SaifYasir/PicoWOL/src/wifi/wifi.c

#include <string.h>

#include "pico/stdlib.h"
#include "pico/cyw43_arch.h"
#include "pico/util/queue.h"

#include "wifi.h"
#include "wol/wol.h"

#include "lwip/pbuf.h"
#include "lwip/udp.h"
#include "lwip/netif.h"
#include "lwip/ip4.h"


machine_stack* default_udp_polling_machine_stack = NULL;
struct udp_pcb* pcb = NULL;

int send_wol_packet_string(char* mac_address_string);
int send_wol_packet(machine* machine);

int initialise_udp_pcb(){
    pcb = udp_new();
    if(udp_bind(pcb, IP_ADDR_ANY, UDP_PORT_NUMBER) == ERR_USE)
    {
        return ERR_USE;
    }
}

int start_wifi(wifi_credential* wifi_credential){
    cyw43_arch_enable_sta_mode();
    return cyw43_arch_wifi_connect_blocking(
        wifi_credential->ssid,
        wifi_credential->ssid_password,
        CYW43_AUTH_WPA2_AES_PSK);
}

void recieve_packet_server(void *arg, struct udp_pcb *pcb, struct pbuf *p, const ip_addr_t *addr, u16_t port){
    // Decipher packet into 1 of 3 options,
    // index, string, mac address
    printf("Received packet: %s",p->payload);
    char first_char = *((char*)(p->payload));
    if (first_char == INDEX_SERVER_DELIMITER)
    {
        // assume this means index
        int index = atoi((char*)(p->payload)+1);
        machine* machine = get_machine_at_index(default_wol_profiles,index);

        //Add packet to polling thing
        push_to_machine_stack(&default_udp_polling_machine_stack,machine);
    }
    else if(first_char == STRING_SERVER_DELIMITER){
        uint8_t machine_profile_size = get_machine_stack_amount(default_wol_profiles);
        for (size_t i = 0; i < machine_profile_size; i++)
        {
            machine* machine = get_machine_at_index(default_wol_profiles,i);
            char* machine_name = machine->machine_name;
            printf("\nString to compare is %s",(char*)(p->payload)+1);
            printf("\nMachine name is: %s",machine_name);

            printf("Rando output %s",strstr((char*)(p->payload),machine_name));
            if(strstr(machine_name,(char*)(p->payload) + 1) != NULL){
                send_wol_packet(machine);
            }
        }
    }
    else if(first_char == MAC_SERVER_DELIMITER){
        send_wol_packet_string((char*)(p->payload)+1);
        // assume mac address is given in straight order IE A61421
    }
    
}

int start_udp_server(){
    if(pcb == NULL){
        initialise_udp_pcb();
    }
    udp_recv(pcb,recieve_packet_server,NULL);
}

int pico_get_port_number(){
    return UDP_PORT_NUMBER;
}

void pico_get_mac_address(uint8_t mac[6]){
    cyw43_wifi_get_mac(&cyw43_state,CYW43_ITF_STA,mac);
}

void pico_get_ip_address(char* data){
    u32_t addr = netif_default->ip_addr.addr  & netif_default->netmask.addr;
    ip4_addr_t* ip_address = netif_ip4_addr(netif_default);
    char* ip_address_str = ipaddr_ntoa(ip_address);
    memcpy(data,ip_address_str,strlen(ip_address_str) + 1);
}


int send_wol_packet(machine* machine){
    uint8_t wol_packet[MAGIC_PACKET_BYTES];
    get_magic_packet(machine,wol_packet);

    if(pcb == NULL){
        initialise_udp_pcb();
    }

    ip_addr_t target_addr;
    ip_addr_t broadcast_address;
    
    // get broadcast address
    broadcast_address.addr = (netif_default->ip_addr.addr & netif_default->netmask.addr) | ~netif_default->netmask.addr;
    udp_connect(pcb,&broadcast_address,UDP_PORT_NUMBER);

    struct pbuf *p = pbuf_alloc(PBUF_TRANSPORT,MAGIC_PACKET_BYTES,PBUF_RAM);
    pbuf_take(p,wol_packet,MAGIC_PACKET_BYTES);
    
    err_t er = udp_send(pcb,p);
    cyw43_arch_poll();

    pbuf_free(p);
    udp_disconnect(pcb);
    return er;
}

int send_wol_packet_string(char* mac_address_string){
    uint8_t wol_packet[MAGIC_PACKET_BYTES];
    uint8_t mac_address[6];

    size_t hex_string_length = strlen(mac_address_string);
    printf("mac address is %s",mac_address_string);
    printf("Size is %d",sizeof(mac_address) * 2);
    if(hex_string_length != (sizeof(mac_address) * 2)){
       printf("Hex string to byte array invalid input!");
       return 1;
    }
    for(size_t i = 0; i < hex_string_length; i += 2){
        sscanf(mac_address_string + i, "%2hhx", &mac_address[i/2]);
    }

    get_magic_packet_mac_addr(mac_address,wol_packet);

    if(pcb == NULL){
        initialise_udp_pcb();
    }

    ip_addr_t target_addr;
    ip_addr_t broadcast_address;
    
    // get broadcast address
    broadcast_address.addr = (netif_default->ip_addr.addr & netif_default->netmask.addr) | ~netif_default->netmask.addr;
    udp_connect(pcb,&broadcast_address,UDP_PORT_NUMBER);

    struct pbuf *p = pbuf_alloc(PBUF_TRANSPORT,MAGIC_PACKET_BYTES,PBUF_RAM);
    pbuf_take(p,wol_packet,MAGIC_PACKET_BYTES);
    
    err_t er = udp_send(pcb,p);
    cyw43_arch_poll();

    pbuf_free(p);
    udp_disconnect(pcb);
    return er;
}

void poll_udp_packets(machine_stack** machine_polling_stack){
    int stack_size = get_machine_stack_amount(*machine_polling_stack);
    for (int i = 0; i < stack_size; i++)
    {
        machine* machine_to_wake = pop_machine_stack(machine_polling_stack);
        send_wol_packet(machine_to_wake);
    }
}
